cuspaceflight/Engine-Test-Stand-Instrumentation/Software/laptop/protocol_v4.py

"""
protocol_v3.py — Serial protocol between the laptop GUI and the ESP32-S3.

All messages are ASCII text terminated with newline ('\\n').
This module is the SINGLE SOURCE OF TRUTH for the wire format.
The ESP32 firmware (main_v3.cpp) implements the matching contract.

Architecture note (v3):
    Sensor data now originates on the instrumentation board and travels
    to this ESP32 over CAN bus. The ESP32 decodes each CAN frame and
    forwards the result as a SENSOR: line over USB serial — identical
    in format to v1. The GUI does not need to know that the transport
    changed; the USB protocol is unchanged in any breaking way.

--- v3.1 ADDITIONS (safety) -------------------------------------------------
Three additive commands and one message support a firmware-side fail-safe.
They are backward compatible at the wire level (new verbs only), BUT the
v3.1 firmware REQUIRES the v3.1 GUI: the firmware now fails safe if it does
not hear from the GUI. Deploy firmware and GUI together — see CODE_OVERVIEW.

    GUI → ESP32   "PING\\n"     liveness keepalive (GUI sends ~2 Hz). Silent
                               on the firmware side — produces no reply, so
                               it never disturbs the OK/ERROR ack stream.
    GUI → ESP32   "ABORT\\n"    atomic safe-state: firmware drives ALL servos
                               to their configured safe position and LATCHES
                               a fail-safe state (servo moves rejected) until
                               re-armed. Replies "OK".
    GUI → ESP32   "RESET\\n"    re-arm after an ABORT / comms-loss latch.
                               Replies "OK" and "STATE:ARMED".
    ESP32 → GUI   "STATE:ARMED\\n"            firmware is armed (servos live)
    ESP32 → GUI   "STATE:FAILSAFE:<reason>\\n" firmware is latched safe
                               (reason e.g. "boot", "abort", "linkloss").
                               Sent on every transition and repeated at 1 Hz
                               so a GUI that connects mid-stream learns state.
-----------------------------------------------------------------------------

GUI → ESP32 (Commands):
    SRV1:500\\n / :1500 / :2500      Servo 1 pulse width in µs
    SRV2:... / SRV3:... / SRV4:...
    SOL1:ON\\n / SOL1:OFF\\n          Solenoid 1 (returns ERROR — no driver on v2 board)
    SOL2:ON\\n / SOL2:OFF\\n          Solenoid 2 (returns ERROR — no driver on v2 board)
    STATUS\\n                         Request full status
    PING\\n / ABORT\\n / RESET\\n      see v3.1 additions above

ESP32 → GUI (Messages):
    OK\\n                             Command acknowledged
    ERROR:<text>\\n                   Error description
    FAULT:1:<0|1>\\n                  CAN bus health: 1=link to instr board OK,
                                     0=no heartbeat for >3 s (was nFAULT in v1)
    SENSOR:<name>:<value>\\n          Sensor reading forwarded from CAN
                                       PRESS1–PRESS8 (bar, after calibration)
                                       TEMP1–TEMP4   (°C, after calibration)
                                       FORCE         (N, after calibration)
    STATE:ARMED\\n / STATE:FAILSAFE:<reason>\\n   arm/fail-safe state (v3.1)
    STATUS:SRV1:<µs>:...:CAN:<OK|FAULT>:STATE:<ARMED|FAILSAFE>\\n
"""
from dataclasses import dataclass


# ═══════════════════════════════════════════════════════════════
# COMMANDS  (GUI → ESP32)
# ═══════════════════════════════════════════════════════════════

class Command:
    """Base class for all commands sent to the ESP32."""

    def to_bytes(self) -> bytes:
        return self.to_str().encode("utf-8")

    def to_str(self) -> str:
        raise NotImplementedError("Subclasses must implement to_str()")


@dataclass
class SolenoidCommand(Command):
    """Energise or de-energise a solenoid via the J6 expansion header.

    NOTE (v2 board): The MPQ6610 solenoid driver chips are not fitted on
    this PCB revision. Sending this command returns an ERROR response.
    Solenoid control will be re-enabled once the J6 expansion daughterboard
    is designed and connected. The command class is kept so the GUI's
    toggle and revert logic does not need to change.
    """
    channel: int   # 1 or 2
    on: bool

    def __post_init__(self):
        if self.channel not in (1, 2):
            raise ValueError(f"Solenoid channel must be 1 or 2, got {self.channel}")

    def to_str(self) -> str:
        state = "ON" if self.on else "OFF"
        return f"SOL{self.channel}:{state}\n"


@dataclass
class ServoCommand(Command):
    """Move a servo to one of three preset positions.

    FT5330M servo at 50 Hz PWM:
        500 µs  = fully closed
        1500 µs = centre
        2500 µs = fully open
    """
    channel: int       # 1–4
    pulse_us: int      # 500, 1500, or 2500

    def __post_init__(self):
        if not 1 <= self.channel <= 4:
            raise ValueError(f"Servo channel must be 1–4, got {self.channel}")
        if self.pulse_us not in (500, 1500, 2500):
            raise ValueError(
                f"Pulse must be 500, 1500, or 2500, got {self.pulse_us}"
            )

    def to_str(self) -> str:
        return f"SRV{self.channel}:{self.pulse_us}\n"


@dataclass
class StatusCommand(Command):
    """Request the ESP32 to report current state of all channels."""

    def to_str(self) -> str:
        return "STATUS\n"


# ── v3.1 safety commands ─────────────────────────────────────────────────────

@dataclass
class PingCommand(Command):
    """Liveness keepalive. The GUI sends this on a timer (~2 Hz) so the
    firmware's operator-link watchdog can tell the GUI is still alive even
    when the operator is not clicking anything. The firmware does not reply,
    so PING never appears in the OK/ERROR ack stream."""

    def to_str(self) -> str:
        return "PING\n"


@dataclass
class AbortCommand(Command):
    """Atomic abort. One frame on the wire; the firmware drives all servos
    to their configured safe state and latches a fail-safe state. Preferred
    over sending four individual SRV:500 commands, which can partially fail."""

    def to_str(self) -> str:
        return "ABORT\n"


@dataclass
class ResetCommand(Command):
    """Re-arm after an abort or a comms-loss latch. The firmware will only
    accept this if the operator link is currently alive."""

    def to_str(self) -> str:
        return "RESET\n"


# ═══════════════════════════════════════════════════════════════
# MESSAGES  (ESP32 → GUI)
# ═══════════════════════════════════════════════════════════════

class Message:
    """Base class for all messages received from the ESP32."""
    pass


@dataclass
class FaultMessage(Message):
    """Health status from the ESP32.

    In v3, channel 1 indicates CAN bus health to the instrumentation board:
        ok=True   last heartbeat (CAN frame 0x010) arrived within 3 seconds
        ok=False  no heartbeat for >3 s — check CAN wiring and instr. board

    Channel 2 is no longer used (was MPQ6610 nFAULT in v1) and is ignored
    by the GUI. The firmware does not emit FAULT:2: messages.
    """
    channel: int
    ok: bool


@dataclass
class SensorMessage(Message):
    """Sensor reading forwarded from the instrumentation board via CAN.

    Names: PRESS1–PRESS8 (bar), TEMP1–TEMP4 (°C), FORCE (N).
    Values are raw counts until calibration.h on the ESP32 is filled in.
    """
    name: str
    value: float


@dataclass
class AckMessage(Message):
    """ESP32 acknowledged a command (sent 'OK')."""
    pass


@dataclass
class ErrorMessage(Message):
    """Error reported by ESP32."""
    message: str


@dataclass
class StatusMessage(Message):
    """Full status report. Raw line preserved for the log."""
    raw: str


@dataclass
class StateMessage(Message):
    """Arm / fail-safe state of the firmware (v3.1).

    state:  "ARMED" or "FAILSAFE"
    reason: free-text reason for a FAILSAFE state ("boot", "abort",
            "linkloss", ...); empty for ARMED.
    """
    state: str
    reason: str = ""


@dataclass
class UnknownMessage(Message):
    """Safety net for any line we could not parse.

    Firmware diagnostic lines (INFO:, WARNING:) arrive as UnknownMessage
    and are logged verbatim by the GUI with an '<unparsed>' prefix.
    """
    raw: str


# ═══════════════════════════════════════════════════════════════
# PARSER  (raw serial line → typed Message)
# ═══════════════════════════════════════════════════════════════

def parse_response(line: str) -> Message:
    """Parse one line from the ESP32 into a typed Message.

    Robust to malformed input — never raises. Anything we cannot
    parse becomes an UnknownMessage so the read loop keeps running.
    """
    line = line.strip()

    if not line:
        return UnknownMessage(raw="")

    # ── FAULT:<channel>:<0|1> ──
    if line.startswith("FAULT:"):
        try:
            parts = line.split(":")
            if len(parts) != 3:
                return UnknownMessage(raw=line)
            return FaultMessage(channel=int(parts[1]), ok=(parts[2] == "1"))
        except (ValueError, IndexError):
            return UnknownMessage(raw=line)

    # ── SENSOR:<name>:<value> ──
    if line.startswith("SENSOR:"):
        try:
            parts = line.split(":")
            if len(parts) != 3:
                return UnknownMessage(raw=line)
            return SensorMessage(name=parts[1], value=float(parts[2]))
        except (ValueError, IndexError):
            return UnknownMessage(raw=line)

    # ── STATE:ARMED  /  STATE:FAILSAFE:<reason> ──  (v3.1)
    if line.startswith("STATE:"):
        parts = line.split(":", 2)   # at most 3 fields: STATE, state, reason
        state = parts[1] if len(parts) > 1 else ""
        reason = parts[2] if len(parts) > 2 else ""
        return StateMessage(state=state, reason=reason)

    # ── OK ──
    if line == "OK":
        return AckMessage()

    # ── ERROR:<text> ──
    if line.startswith("ERROR:"):
        return ErrorMessage(message=line[6:])

    # ── STATUS:... ──
    if line.startswith("STATUS:"):
        return StatusMessage(raw=line)

    # Anything else (firmware boot banner, INFO:, WARNING:, ...)
    return UnknownMessage(raw=line)
